Piottry/C_Bastien/Shematic/Robot_Schematic.kicad_sch

## KiCad design Shematic/Robot_Schematic.kicad_sch (2023-01-29)

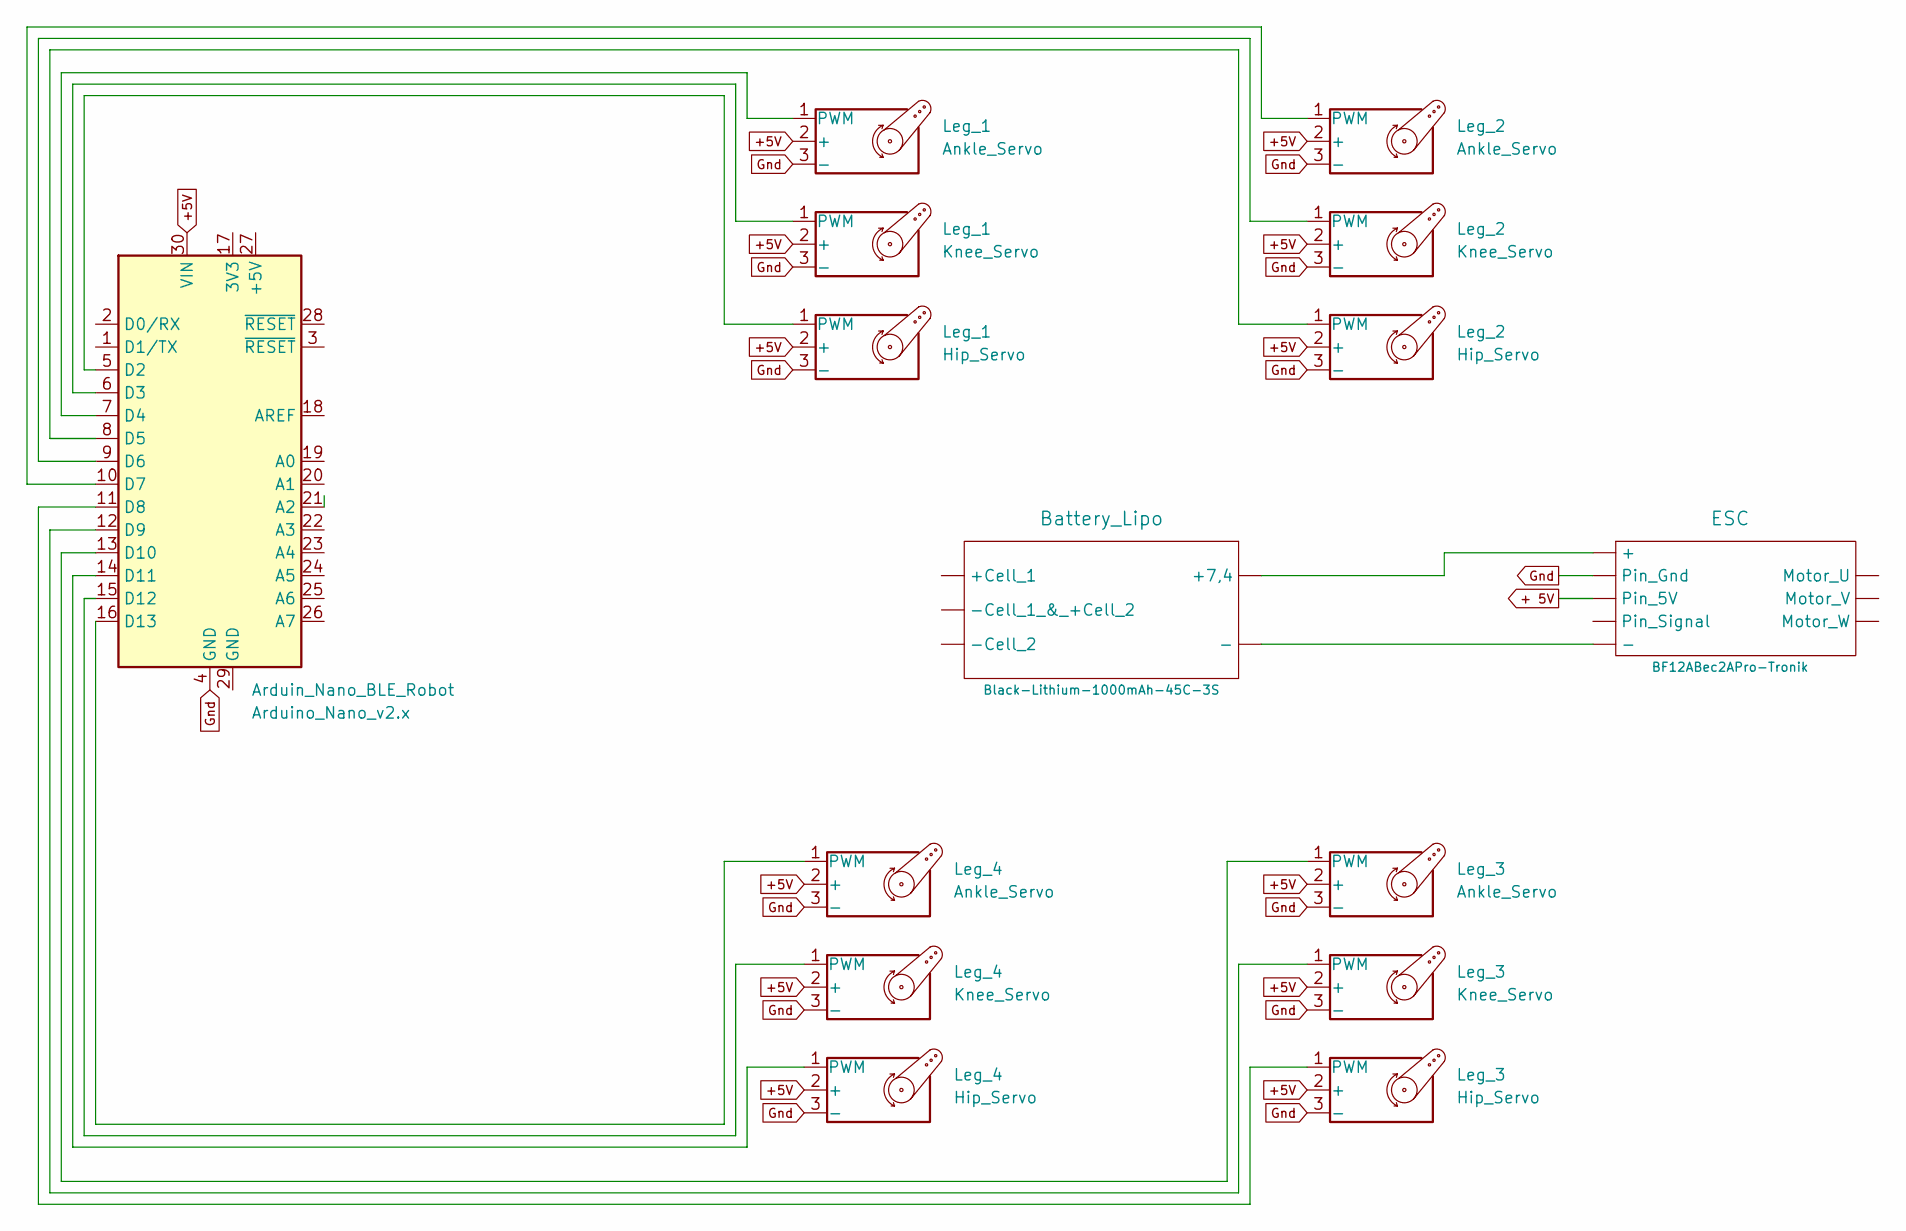
[picture p26: schematic Robot_Schematic.kicad_sch]

Parts:
Arduin_Nano_BLE_Robot: Arduino_Nano_v2.x; Arduino_Nano
BF12ABec2APro-Tronik: ESC
Black-Lithium-1000mAh-45C-3S: Battery_Lipo
Leg_1, Leg_3: Ankle_Servo
Leg_2: Knee_Servo
Leg_4: Hip_Servo

Connections:
+5V: Arduin_Nano_BLE_Robot.30 (VIN), Leg_1.2 (+), Leg_2.2 (+), Leg_3.2 (+), Leg_4.2 (+)
+ 5V: BF12ABec2APro-Tronik.
Gnd: Arduin_Nano_BLE_Robot.4 (GND), BF12ABec2APro-Tronik., Leg_1.3 (-), Leg_2.3 (-), Leg_3.3 (-), Leg_4.3 (-)
unnamed: Arduin_Nano_BLE_Robot.5 (D2), Leg_1.1 (PWM)
unnamed: Arduin_Nano_BLE_Robot.6 (D3), Leg_1.1 (PWM)
unnamed: Arduin_Nano_BLE_Robot.7 (D4), Leg_1.1 (PWM)
unnamed: Arduin_Nano_BLE_Robot.8 (D5), Leg_2.1 (PWM)
unnamed: Arduin_Nano_BLE_Robot.9 (D6), Leg_2.1 (PWM)
unnamed: Arduin_Nano_BLE_Robot.10 (D7), Leg_2.1 (PWM)
unnamed: Arduin_Nano_BLE_Robot.11 (D8), Leg_3.1 (PWM)
unnamed: Arduin_Nano_BLE_Robot.12 (D9), Leg_3.1 (PWM)
unnamed: Arduin_Nano_BLE_Robot.13 (D10), Leg_3.1 (PWM)
unnamed: Arduin_Nano_BLE_Robot.14 (D11), Leg_4.1 (PWM)
unnamed: Arduin_Nano_BLE_Robot.15 (D12), Leg_4.1 (PWM)
unnamed: Arduin_Nano_BLE_Robot.16 (D13), Leg_4.1 (PWM)
unnamed: BF12ABec2APro-Tronik., Black-Lithium-1000mAh-45C-3S.
